ceezblog/T12-Solder-station/Enclosure/standalone iron handle stand.png

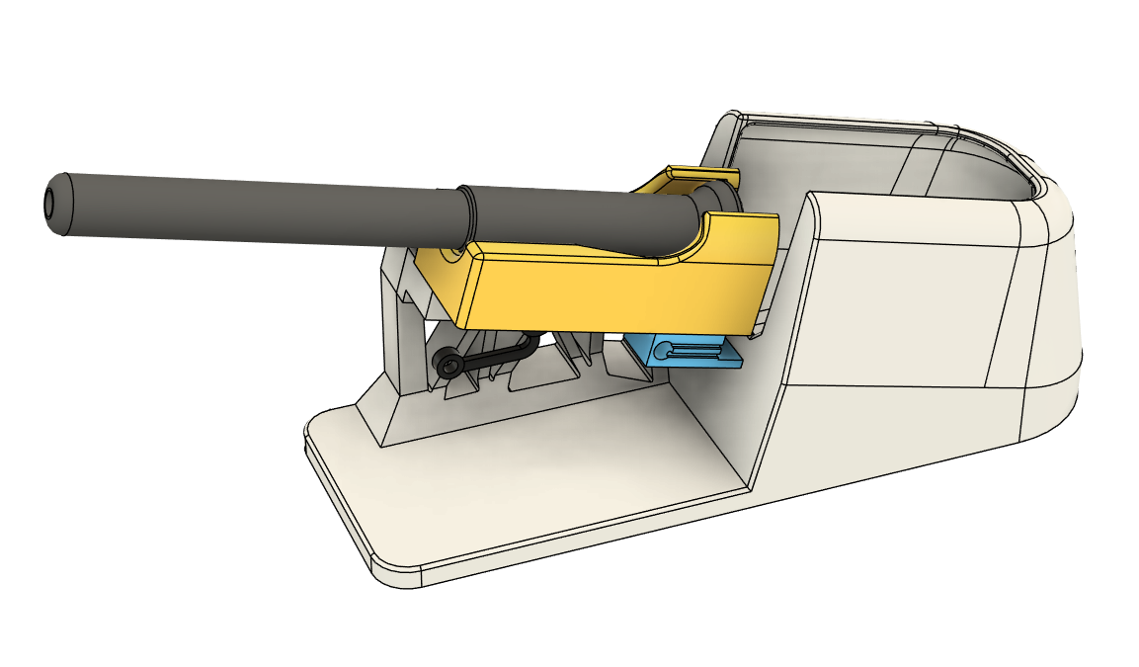
Enclosure/standalone iron handle stand.png
