ceezblog/T12-Solder-station/PCB/Buck Mini360.jpg

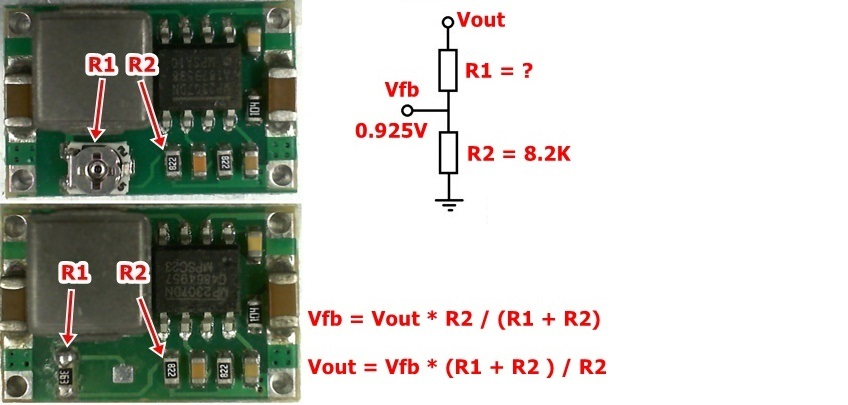
PCB/Buck Mini360.jpg
