ceezblog/T12-Solder-station/PCB/Render 1.png

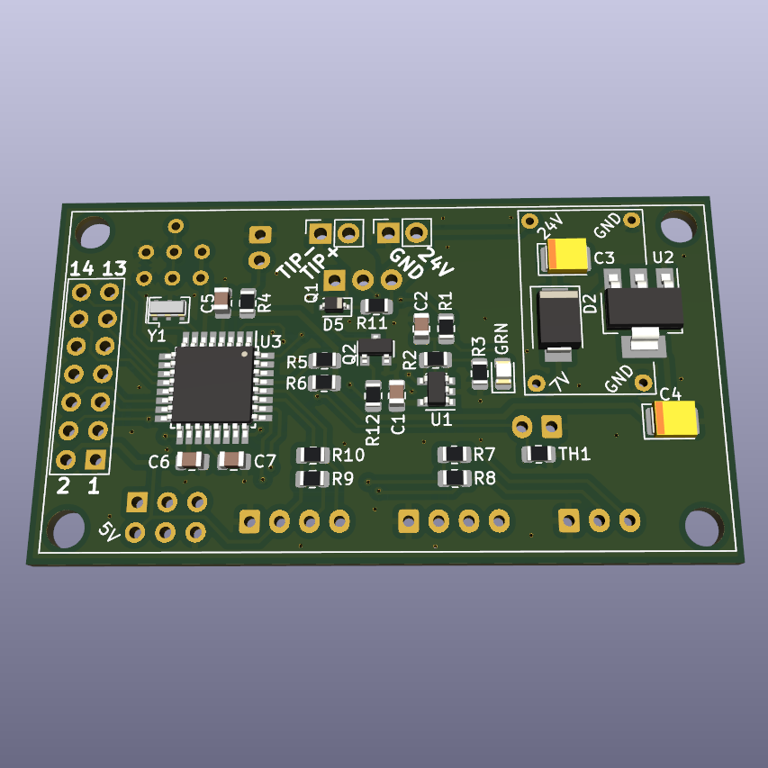
PCB/Render 1.png
