ceezblog/T12-Solder-station/PCB/Render 2.png

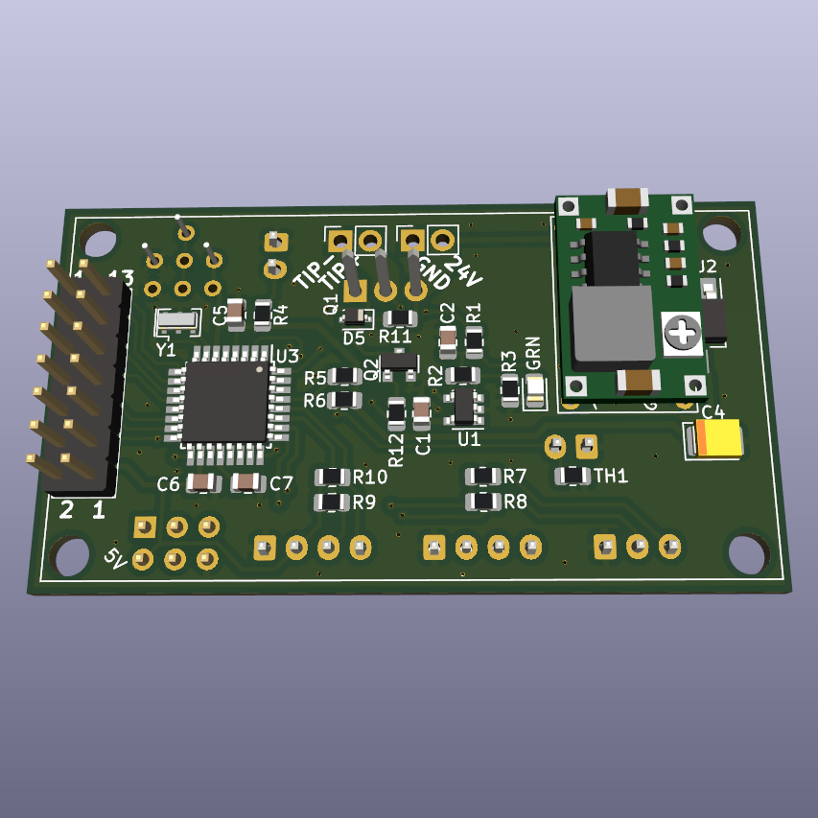
PCB/Render 2.png
