ceezblog/T12-Solder-station/PSU/WX-DC2412_Bottom.png

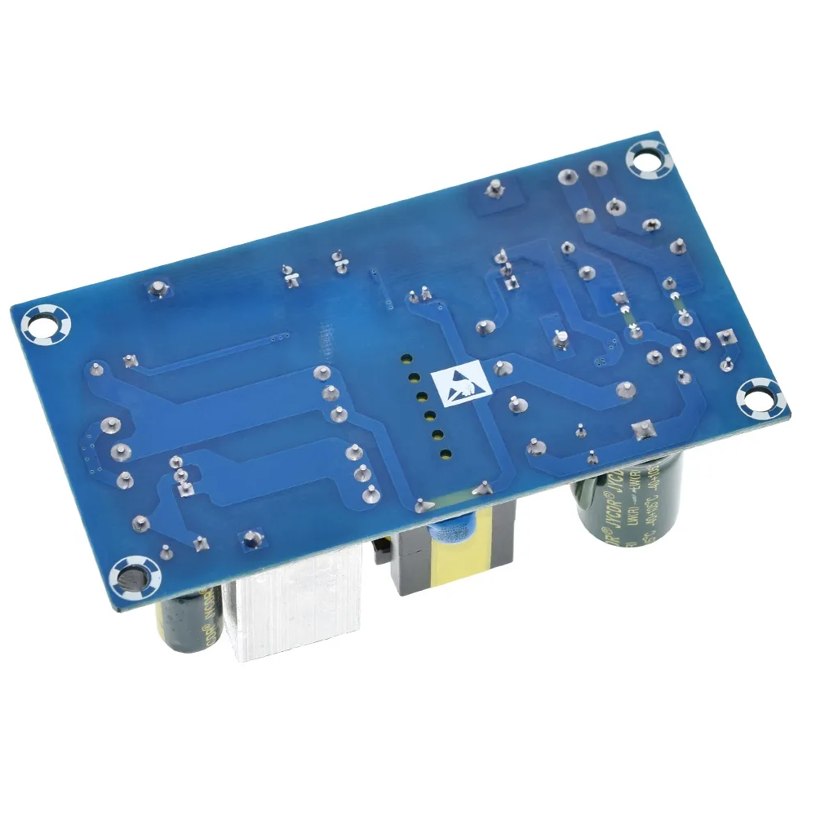
PSU/WX-DC2412_Bottom.png
