ceezblog/T12-Solder-station/PSU/WX-DC2412_Dimensions.jpg

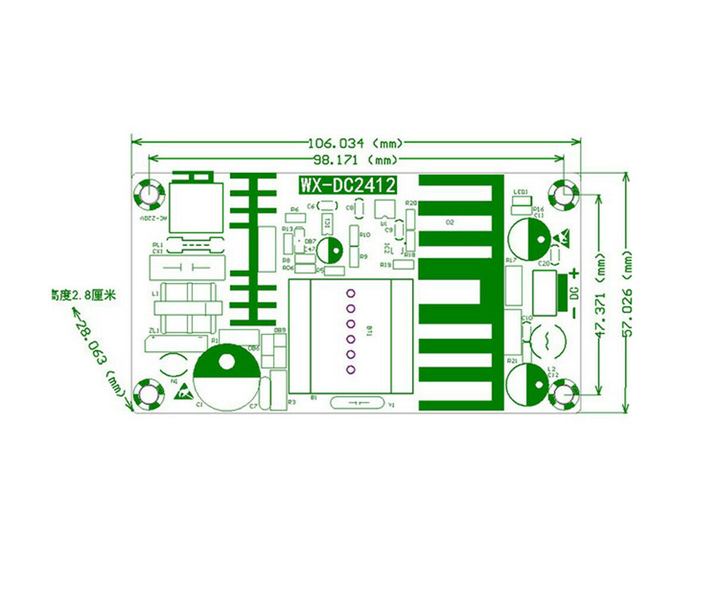
PSU/WX-DC2412_Dimensions.jpg
