ceezblog/T12-Solder-station/PSU/XK-2412DC.png

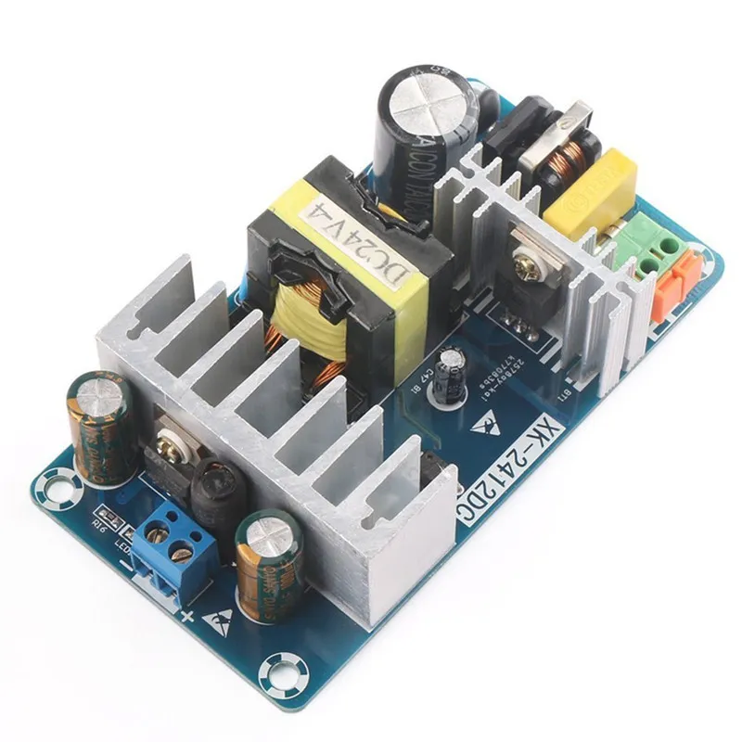
PSU/XK-2412DC.png
